zwenergy/gbaHD/hdl/imageGen.sv

//-----------------------------------------------------------------------
//-- Title: Image Gen
//-- Author: zwenergy
//-----------------------------------------------------------------------

import definePackage::*;

module imageGenV
(
  input logic pxlClk,
  input logic pxlClk5x,
  input logic rst,
  
  input logic [7:0] prevLinePrevPxlRedIn,
  input logic [7:0] prevLinePrevPxlGreenIn,
  input logic [7:0] prevLinePrevPxlBlueIn,
  input logic [7:0] prevLineCurPxlRedIn,
  input logic [7:0] prevLineCurPxlGreenIn,
  input logic [7:0] prevLineCurPxlBlueIn,
  input logic [7:0] prevLineNextPxlRedIn,
  input logic [7:0] prevLineNextPxlGreenIn,
  input logic [7:0] prevLineNextPxlBlueIn,
  input logic [7:0] curLinePrevPxlRedIn,
  input logic [7:0] curLinePrevPxlGreenIn,
  input logic [7:0] curLinePrevPxlBlueIn,
  input logic [7:0] curLineCurPxlRedIn,
  input logic [7:0] curLineCurPxlGreenIn,
  input logic [7:0] curLineCurPxlBlueIn,
  input logic [7:0] curLineNextPxlRedIn,
  input logic [7:0] curLineNextPxlGreenIn,
  input logic [7:0] curLineNextPxlBlueIn,
  input logic [7:0] nextLinePrevPxlRedIn,
  input logic [7:0] nextLinePrevPxlGreenIn,
  input logic [7:0] nextLinePrevPxlBlueIn,
  input logic [7:0] nextLineCurPxlRedIn,
  input logic [7:0] nextLineCurPxlGreenIn,
  input logic [7:0] nextLineCurPxlBlueIn,
  input logic [7:0] nextLineNextPxlRedIn,
  input logic [7:0] nextLineNextPxlGreenIn,
  input logic [7:0] nextLineNextPxlBlueIn,
  
  input logic sameLine,
  input logic newFrameIn,
  input logic audioLIn,
  input logic audioRIn,
  
  input logic osdEnable,
  input logic rxValid,
  input logic [9:0] controller,
  input logic controllerOSDActive,
  
  input logic [7:0] osdState,
  input logic osdStateValid,
  input logic osdSmooth2x,
  input logic osdSmooth4x,
  input logic osdGridActive,
  input logic osdGridBright,
  input logic osdGridMult,
  input logic osdColorCorrection_in,
  input logic osdRate_in,
  input logic osdSettingsValid,
  
  output logic colorMode,
  output logic framerate,
  
  output logic nextLine,
  output logic cacheUpdate,
  output logic [7:0] curPxl,
  
  output logic [2:0] tmds,
  output logic tmdsClk  
);

localparam audioAtten = 1;

wire audioClk_gba, audioValid;
logic [AUDIO_BIT_WIDTH-1:0] pcmL, pcmR;

// Audio module.
pwm2pcm #( .clkFreq0( pxlClkFrq_60hz ),
           .clkFreq1( pxlClkFrq_59hz ),
           .sampleFreq( 48.0 ),
           .atten( audioAtten ),
           // Chosen to be divisible by input and output sample rates:
           // lcm(32768, 48000) / 48000 = 256
           .upsample( 256 ),
           // Determined by testing
           .filter( 8 ) )
pwm2pcm( .pwmInL( audioLIn ), 
         .pwmInR( audioRIn ), 
         .clk( pxlClk ), 
         .rst( rst ), 
         .clkFreq( framerate ),
         .sampleClkOut( audioClk_gba ), 
         .datOutL( pcmL ), 
         .datOutR( pcmR ));


// HDMI.
logic [23:0] rgb;
logic [10:0] cy, frameHeight;
logic [11:0] cx, frameWidth;

logic enableHdmi;

localparam int gbaVideoXStart = ( FRAMEWIDTH - ( maxScaleCnt + 1 ) * 240 ) / 2;
localparam int gbaVideoYStart = ( FRAMEHEIGHT - ( maxScaleCnt + 1 ) * 160 ) / 2;
localparam int gbaVideoXStop = gbaVideoXStart + ( maxScaleCnt + 1 ) * 240;
localparam int gbaVideoYStop = gbaVideoYStart + ( maxScaleCnt + 1 ) * 160;


hdmi #( .VIDEO_ID_CODE(VIDEOID), 
        .DVI_OUTPUT(0), 
        .VIDEO_REFRESH_RATE(VIDEO_REFRESH),
        .IT_CONTENT(1),
        .AUDIO_RATE(48000), 
        .AUDIO_BIT_WIDTH(AUDIO_BIT_WIDTH),
        .START_X(gbaVideoXStart),
        .START_Y(gbaVideoYStart) )
hdmi( .clk_pixel_x5(pxlClk5x), 
      .clk_pixel(pxlClk), 
      .clk_audio(audioClk_gba),
      .rgb(rgb), 
      .reset( rst || !enableHdmi ),
      .audio_sample_word('{pcmR, pcmL}),
      .tmds(tmds), 
      .tmds_clock(tmdsClk), 
      .cx(cx), 
      .cy(cy),
      .frame_width( frameWidth ),
      .frame_height( frameHeight ) );


// Create the image.
logic [2:0] lineCntScale, pxlCntScale, gridXCnt, smoothXCnt;
logic drawGBA;
logic [7:0] redPxlGBA, greenPxlGBA, bluePxlGBA;
logic [7:0] pxlCntRead;
logic [7:0] redPxl, greenPxl, bluePxl, gridRed, gridGreen, gridBlue,
            smoothRed, smoothGreen, smoothBlue, osdRed, osdGreen, osdBlue,
            borderRed, borderGreen, borderBlue;
            
logic drawOSD;
logic pxlGrid;
logic smooth2x, smooth4x;
logic gridAct;
logic brightGrid;
logic gridMult;

always_ff @( posedge pxlClk )
begin
  if ( cx >= gbaVideoXStart && cx < gbaVideoXStop &&
       cy >= gbaVideoYStart && cy < gbaVideoYStop )
    drawGBA <= 1;
  else
    drawGBA <= 0;
  
  if ( cx == gbaVideoXStop && !sameLine &&
       cy >= gbaVideoYStart && lineCntScale == maxScaleCnt )
    nextLine <= 1;
  else
    nextLine <= 0;

  if ( cx == gbaVideoXStop )
    cacheUpdate <= 1;
  else
    cacheUpdate <= 0;
end

assign rgb = { redPxl, greenPxl, bluePxl };
assign curPxl = pxlCntRead;
logic newFrameDel;


always_ff @( posedge pxlClk )
begin
  if ( rst )
  begin
    pxlCntRead <= 8'(0);
    pxlCntScale <= 3'(0);
    lineCntScale <= 3'(0);
    redPxlGBA <= 8'(0);
    greenPxlGBA <= 8'(0);
    bluePxlGBA <= 8'(0);
    enableHdmi <= 0;
    newFrameDel <= 0;
  end
  else
  begin
    if (newFrameIn)
      enableHdmi <= 1;

    newFrameDel <= newFrameIn;
    
    // Some shields offer in-game reset support, hence
    // we should resync if a new frame comes at an unexpected time.
    if ( newFrameIn == 1 && newFrameDel == 0 &&
         !( cy == gbaVideoYStart || cy == gbaVideoYStart - 1 ) )
    begin
      enableHdmi <= 0;
    end

    redPxlGBA <= curLineCurPxlRedIn;
    greenPxlGBA <= curLineCurPxlGreenIn;
    bluePxlGBA <= curLineCurPxlBlueIn;

    if ( cx == gbaVideoXStart || gridXCnt == maxScaleCnt ) begin
      gridXCnt <= 0;
      smoothXCnt <= 1;
    end else begin
      gridXCnt <= gridXCnt + 1;
      smoothXCnt <= smoothXCnt + 1;
    end

    // FIXME: magic constant 3 gets pixel transitions from lineCache to
    // coincide with desired HDMI output, would be good to derive from cycle
    // timings in a more principled way
    `ifdef RES0_480P
    if ( cx > ( gbaVideoXStop - 3 ) && cx < 856 )
    `else
    if ( cx <= gbaVideoXStart - 3 || cx > gbaVideoXStop - 3 )
    `endif
    begin
      pxlCntScale <= 3'(0);
      pxlCntRead <= 8'(0);
    end else begin
      if ( pxlCntScale == maxScaleCnt ) begin
        pxlCntScale <= 0;
        pxlCntRead <= pxlCntRead + 1'b1;
      end else begin
        pxlCntScale <= pxlCntScale + 1'b1;
      end
    end
    
    if ( cx == (frameWidth - 1) )
    begin
      if ( ( cy == ( frameHeight - 1 ) ) )
      begin
        lineCntScale <= 3'(0);
      end else if ( lineCntScale == maxScaleCnt )
      begin
        lineCntScale <= 3'(0);
      end else if ( cy >= gbaVideoYStart ) 
      begin
          lineCntScale <= lineCntScale + 1'b1;
      end
    end
    
  end
end

// Choose which signal outlet.
logic overlayInact;
logic overlayAct;

always_comb
begin
  if( drawOSD ) begin
    redPxl <= osdRed;
    greenPxl <= osdGreen;
    bluePxl <= osdBlue;
    
  end else if ( drawGBA ) begin
    if ( pxlGrid ) begin
      redPxl <= gridRed;
      greenPxl <= gridGreen;
      bluePxl <= gridBlue;
      
    end else if ( ( smooth2x || smooth4x ) && SMOOTHENABLE ) begin
      redPxl <= smoothRed;
      greenPxl <= smoothGreen;
      bluePxl <= smoothBlue;
      
    end else begin
      redPxl <= redPxlGBA;
      greenPxl <= greenPxlGBA;
      bluePxl <= bluePxlGBA;
    end
    
  end else begin
    redPxl <= borderRed;
    greenPxl <= borderGreen;
    bluePxl <= borderBlue;
  end
  
  if ( controllerOSDActive ) begin
    if ( overlayInact ) begin
      redPxl <= 8'b11111111;
      greenPxl <= 8'b11111111;
      bluePxl <= 8'b11111111;
    end

    if ( overlayAct ) begin
      redPxl <= 8'b11111111;
      greenPxl <= 0;
      bluePxl <= 0;
    end
  end
end


// Pixel grid.
assign gridAct = ( gridXCnt == 0 || lineCntScale == 0 );

gridGen #( .ALPHA(2),
           .DELTA(29) )
gridGen ( .pxlInRed( redPxlGBA ),
          .pxlInGreen( greenPxlGBA ),
          .pxlInBlue( bluePxlGBA ),
          .gridAct( gridAct ),
          .brightGrid( brightGrid ),
          .gridMult( gridMult ),
          .pxlOutRed( gridRed ),
          .pxlOutGreen( gridGreen ),
          .pxlOutBlue( gridBlue ) );
          

// Smoothing.
smooth4x ( .rTL( prevLinePrevPxlRedIn ),
           .gTL( prevLinePrevPxlGreenIn ),
           .bTL( prevLinePrevPxlBlueIn ),
           .rTM( prevLineCurPxlRedIn ),
           .gTM( prevLineCurPxlGreenIn ),
           .bTM( prevLineCurPxlBlueIn ),
           .rTR( prevLineNextPxlRedIn ),
           .gTR( prevLineNextPxlGreenIn ),
           .bTR( prevLineNextPxlBlueIn ),
           
           .rCL( curLinePrevPxlRedIn ),
           .gCL( curLinePrevPxlGreenIn ),
           .bCL( curLinePrevPxlBlueIn ),
           .rCM( curLineCurPxlRedIn ),
           .gCM( curLineCurPxlGreenIn ),
           .bCM( curLineCurPxlBlueIn ),
           .rCR( curLineNextPxlRedIn ),
           .gCR( curLineNextPxlGreenIn ),
           .bCR( curLineNextPxlBlueIn ),
           
           .rBL( nextLinePrevPxlRedIn ),
           .gBL( nextLinePrevPxlGreenIn ),
           .bBL( nextLinePrevPxlBlueIn ),
           .rBM( nextLineCurPxlRedIn ),
           .gBM( nextLineCurPxlGreenIn ),
           .bBM( nextLineCurPxlBlueIn ),
           .rBR( nextLineNextPxlRedIn ),
           .gBR( nextLineNextPxlGreenIn ),
           .bBR( nextLineNextPxlBlueIn ),
           
           // FIXME: this module seems to be out of phase with
           // the grid logic, which seems correct (i.e. gridXCnt is
           // 0 on the 1st hdmi pixel corresponding to a GBA pixel)
           .xsel( smoothXCnt[1:0] ),
           .ysel( lineCntScale[1:0] ),
           .do4x( smooth4x ),
           
           .rOut( smoothRed ),
           .gOut( smoothGreen ),
           .bOut( smoothBlue ) );
           
           
// OSD.
osd #( .scale( maxScaleCnt + 1 ),
       .frameWidth( FRAMEWIDTH ),
       .frameHeight( FRAMEHEIGHT ) ) 
osd ( .pxlX( cx ),
      .pxlY( cy ),
//      .controller( controller ),
      .osdEnableIn( osdEnable ),
      .rxValid( rxValid ),
      .clk( pxlClk ),
      .rst( rst ),
      .osdEnableOut( drawOSD ),
      .osdRed( osdRed ),
      .osdGreen( osdGreen ),
      .osdBlue( osdBlue ),
      
      .smooth2xIn( osdSmooth2x ),
      .smooth4xIn( osdSmooth4x ),
      .pixelGridIn( osdGridActive ),
      .bgridIn( osdGridBright ),
      .gridMultIn( osdGridMult ),
      .colorModeIn( osdColorCorrection_in ),
      .rateIn( osdRate_in ),
      .controllerOSDActive( controllerOSDActive ),
      
      .smooth2xOut( smooth2x ),
      .smooth4xOut( smooth4x ),
      .pixelGridOut( pxlGrid ),
      .bgridOut( brightGrid ),
      .gridMultOut( gridMult ),
      .colorModeOut( colorMode ),
      .rateOut( framerate ),
      
      .osdState( osdState ),
      .configValid( osdSettingsValid ),
      .stateValid( osdStateValid )
      );
      
// Pad overlay.
padOverlay #( .posX( 10 ),
              .posY( 10 ),
              .scale( maxScaleCnt + 1 ),
              .frameWidth( FRAMEWIDTH ),
              .frameHeight( FRAMEHEIGHT ) )
padOverlay ( .pxlX( cx ),
             .pxlY( cy ),
             .buttons( controller ),
             .clk( pxlClk ),
             .rst( rst ),
             .overlayInact( overlayInact ),
             .overlayAct( overlayAct ) );

      
// Border gen.
borderGen #( .xMin( 0 ),
             .xMax( widthMax - 1 ),
             .yMin( 0 ),
             .yMax( heightMax - 1 ) )
borderGen ( .x( cx ),
            .y( cy ),
            .r( borderRed ),
            .g( borderGreen ) );


endmodule
